gdex1974/AirSensorExternalESP32/main/AppConfig.h

#pragma once

#include <array>
#include <cstdint>

struct AppConfig
{
    static const std::array<const uint8_t, 6> macAddress;
    static const uint8_t bme280Address;
    // Serial1 is used for debug output
    static const int8_t serial1RxPin;
    static const int8_t serial1TxPin;
    // Serial2 is used for SPS30 communication
    static const int8_t Sps30UartNum;
    static const int8_t sps30RxPin;
    static const int8_t sps30TxPin;
    static const int8_t SDA;
    static const int8_t SCL;
    static const int8_t stepUpPin;
    static const uint8_t voltagePin;
    static const float batteryVoltageDivider;
    static const bool restrictTxPower;
};
